nanofury/NanoFury/NF1/docs/bitfury/discreteshift.pdf

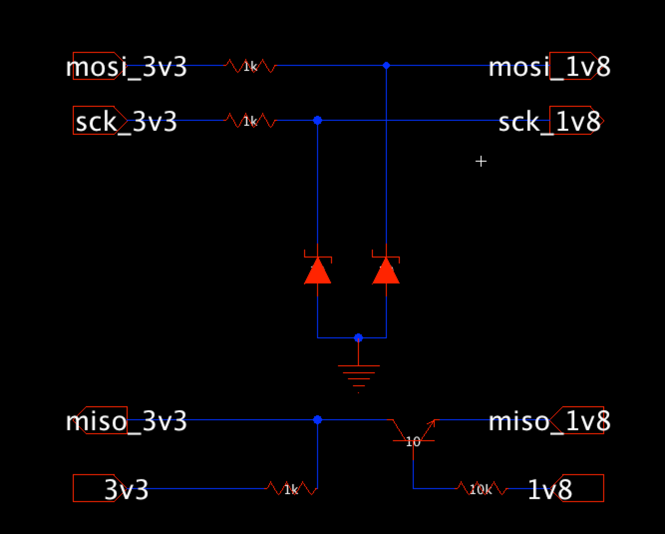
[picture p3: page 1]
