nanofury/NanoFury/NF1/kicad/NF1-MCP-V06/NF1-MCP2210-v06-PCB_Dimensions.pdf

NanoFury NF1 PCB Dimensions

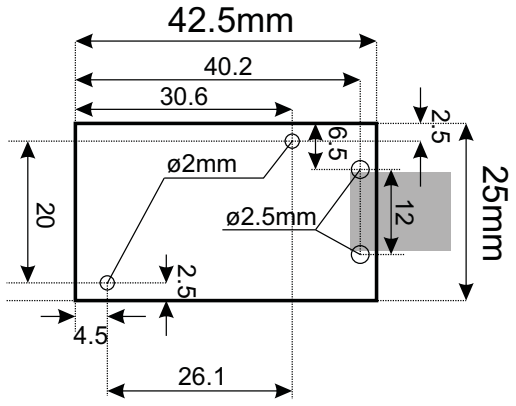
[picture p4: figure]
