nanofury/NanoFury/NF1/kicad/NF1-V0.0/NF1.png

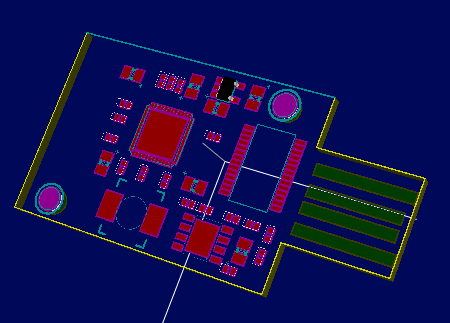
NF1/kicad/NF1-V0.0/NF1.png
