nanofury/NanoFury/NF1/docs/1001-011-01101.pdf

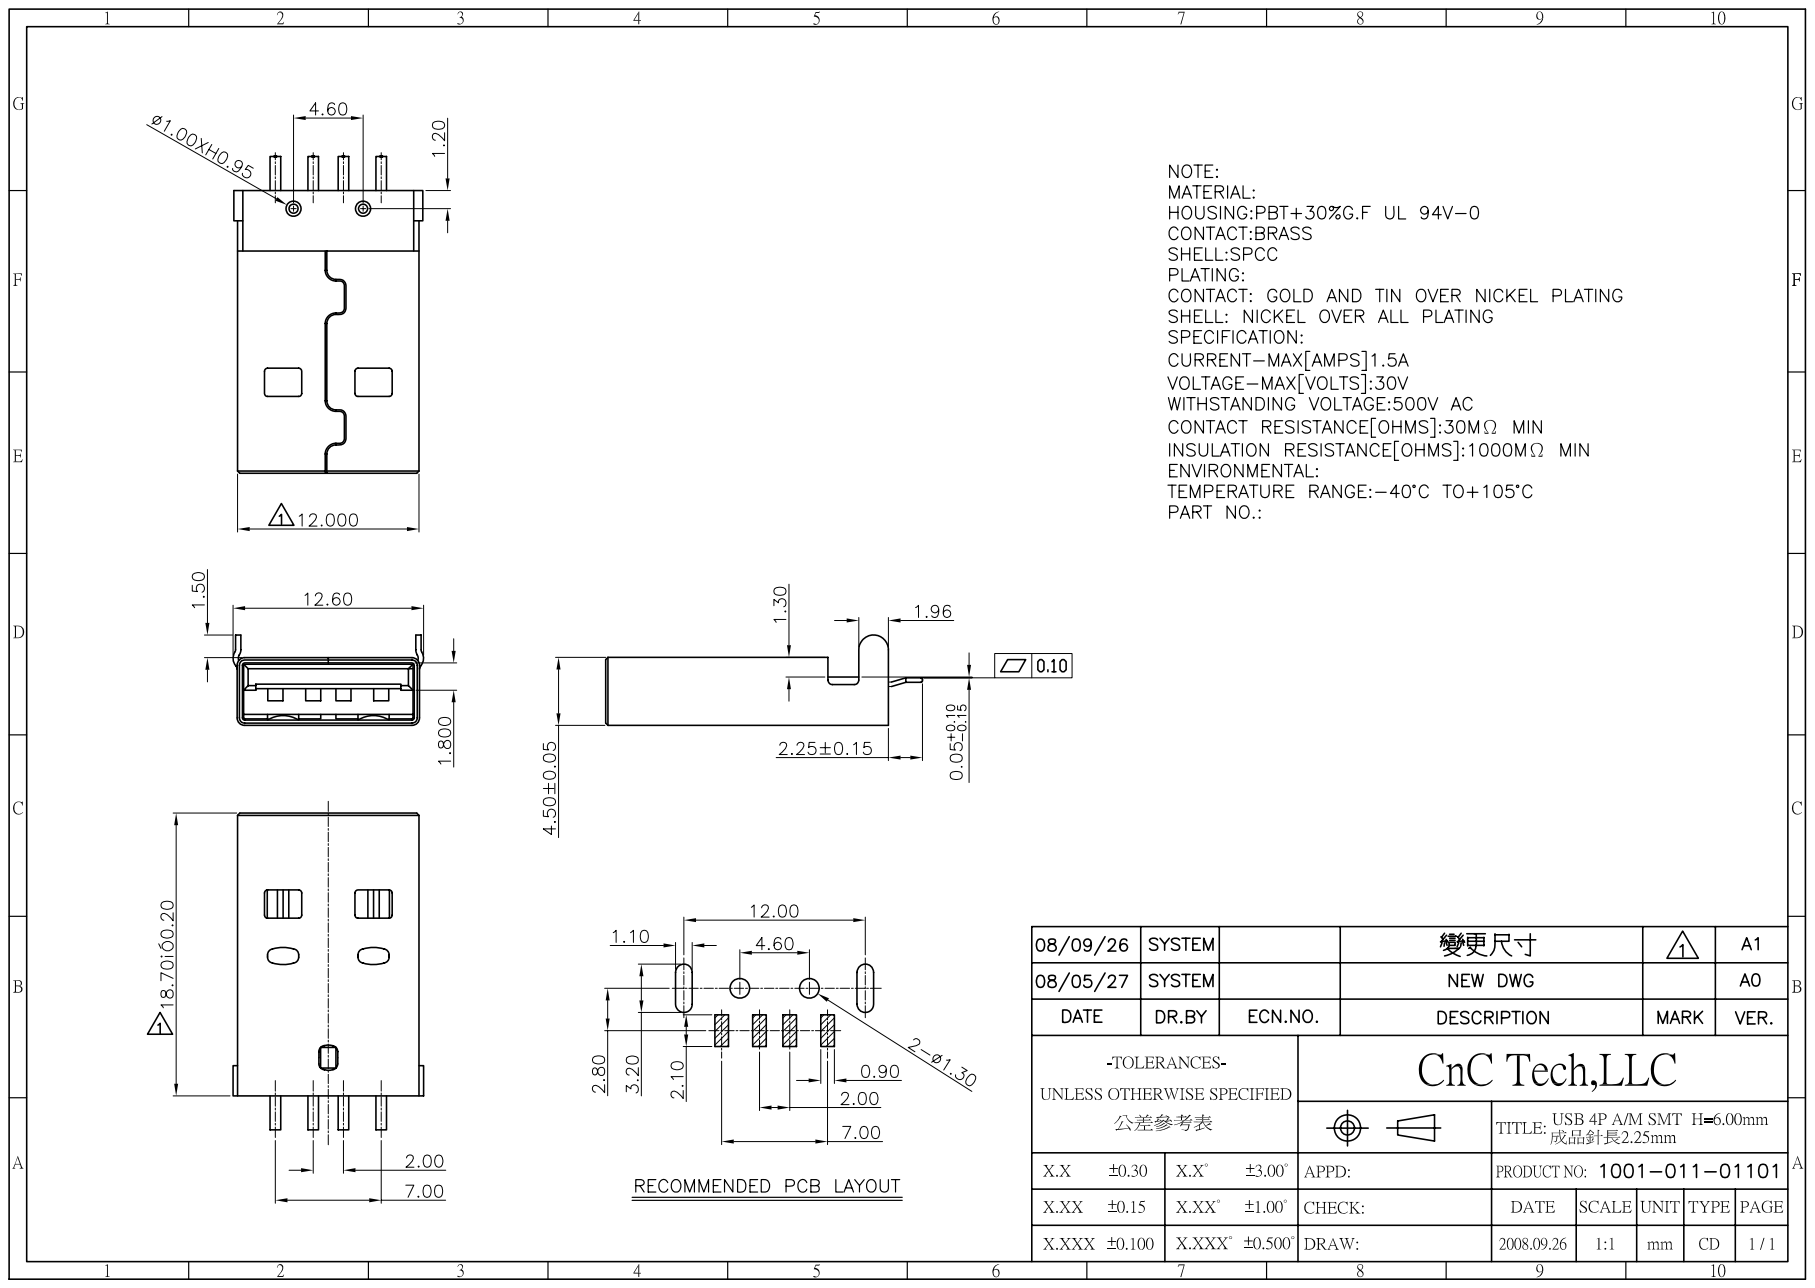
[picture p15: page 1]
