nanofury/NanoFury/NF1/kicad/NF2-MCP-V05/NF2-MCP2210-v05 - SCH.pdf

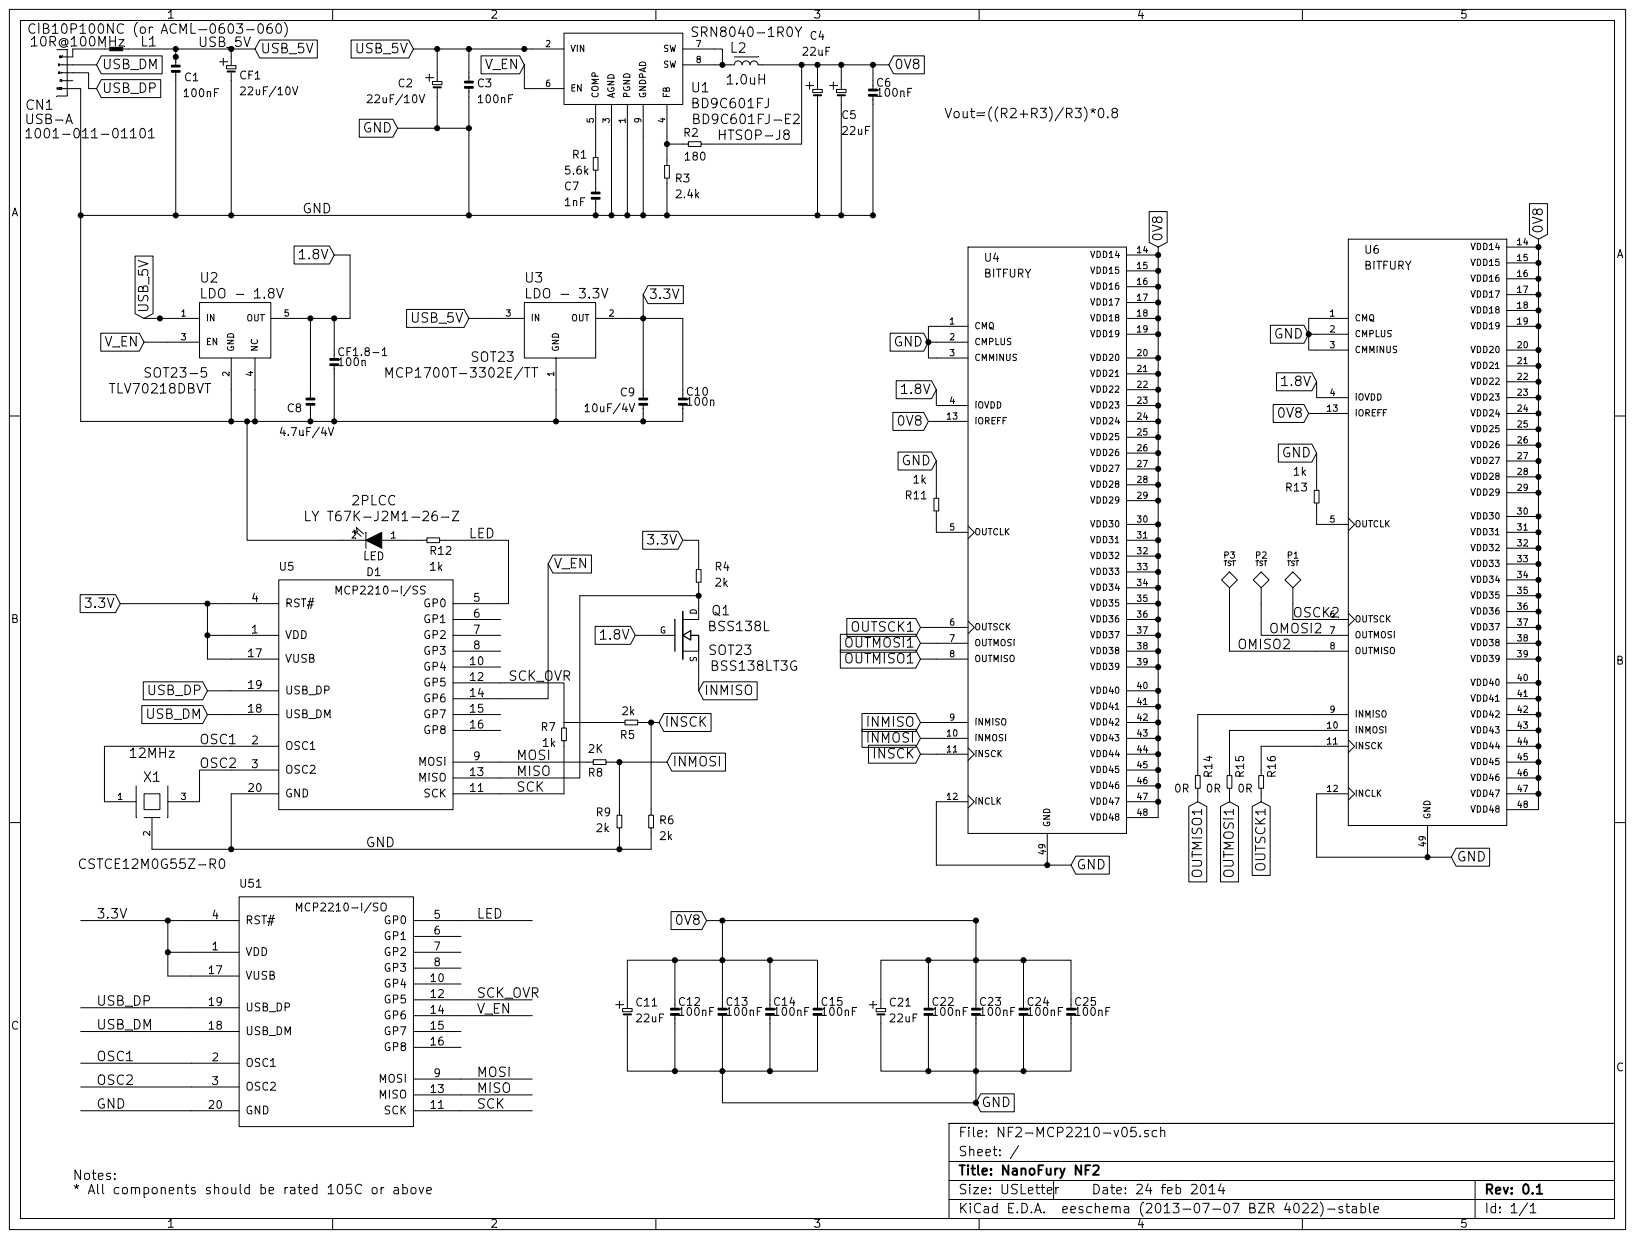
[picture p16: page 1]
