nanofury/NanoFury/NF1/kicad/NF6-MCP-V03/NF6-MCP2210-v03 - SCH.pdf

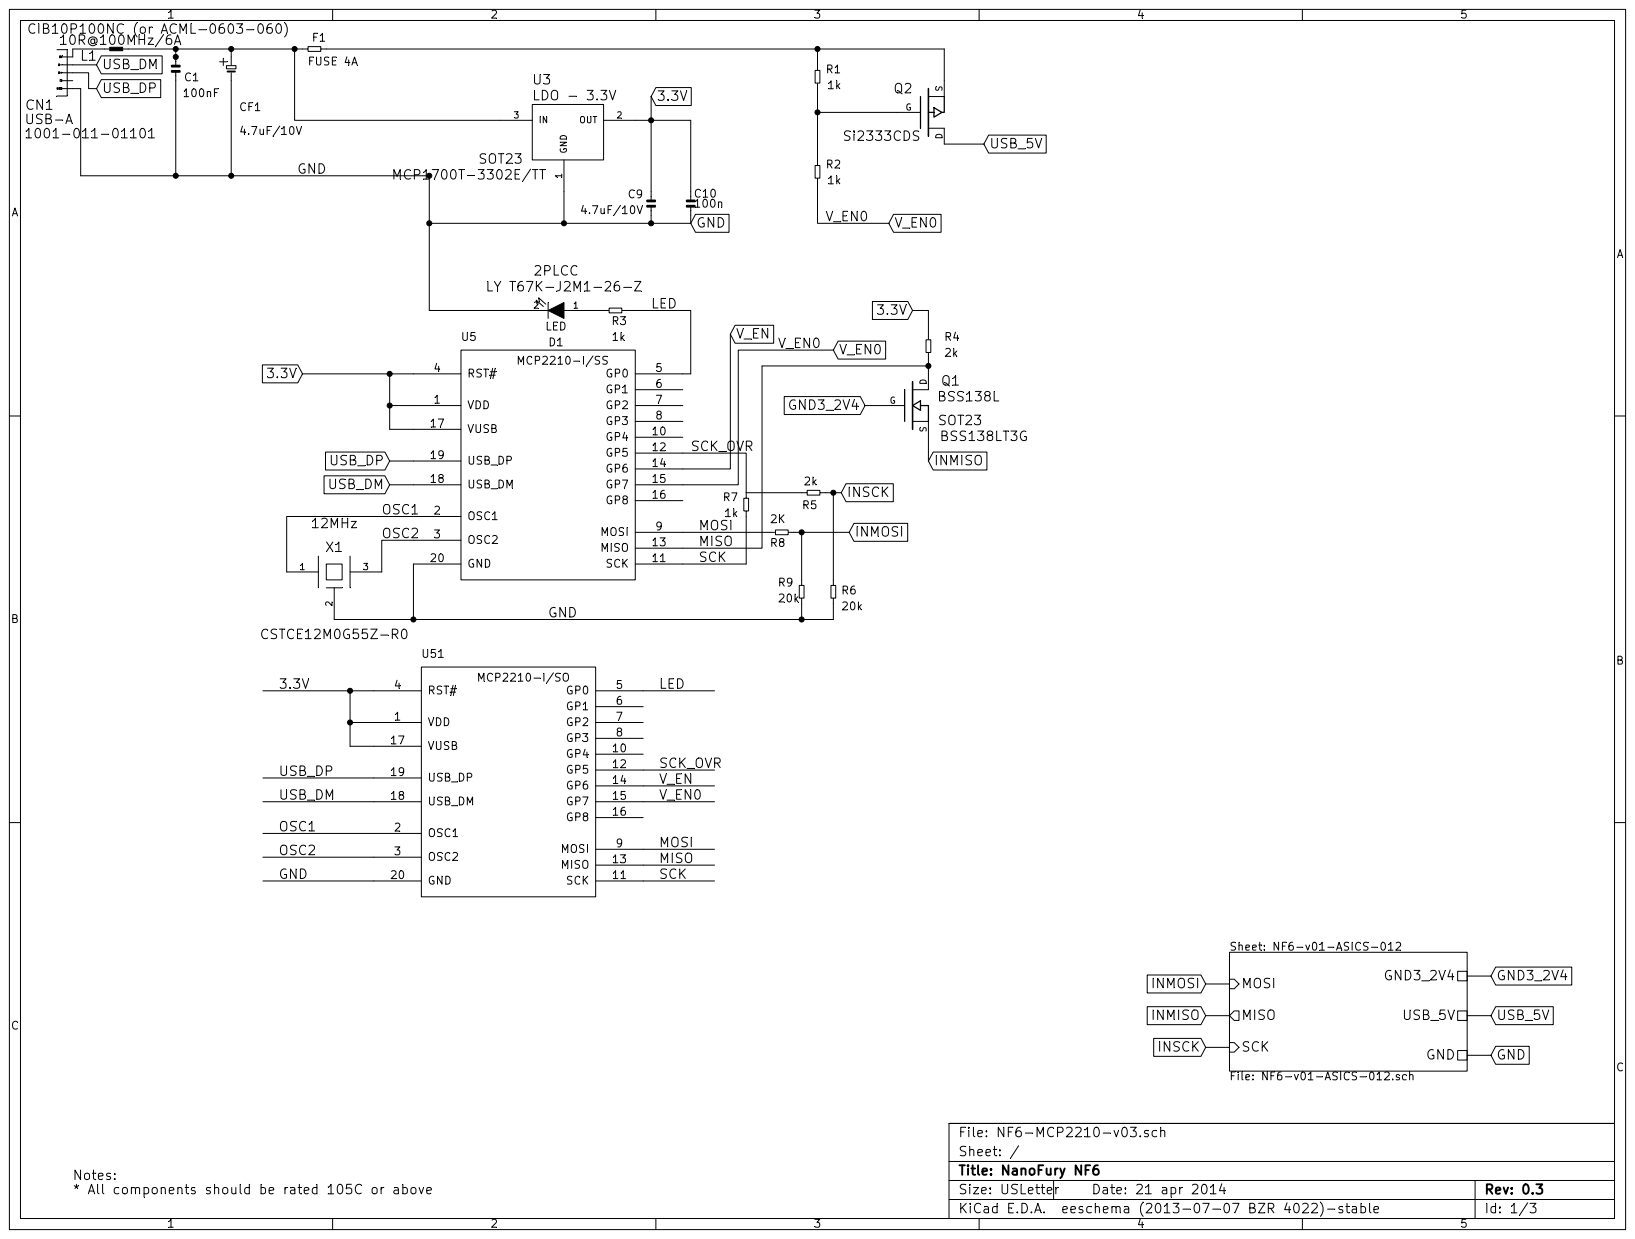
[picture p17: page 1]

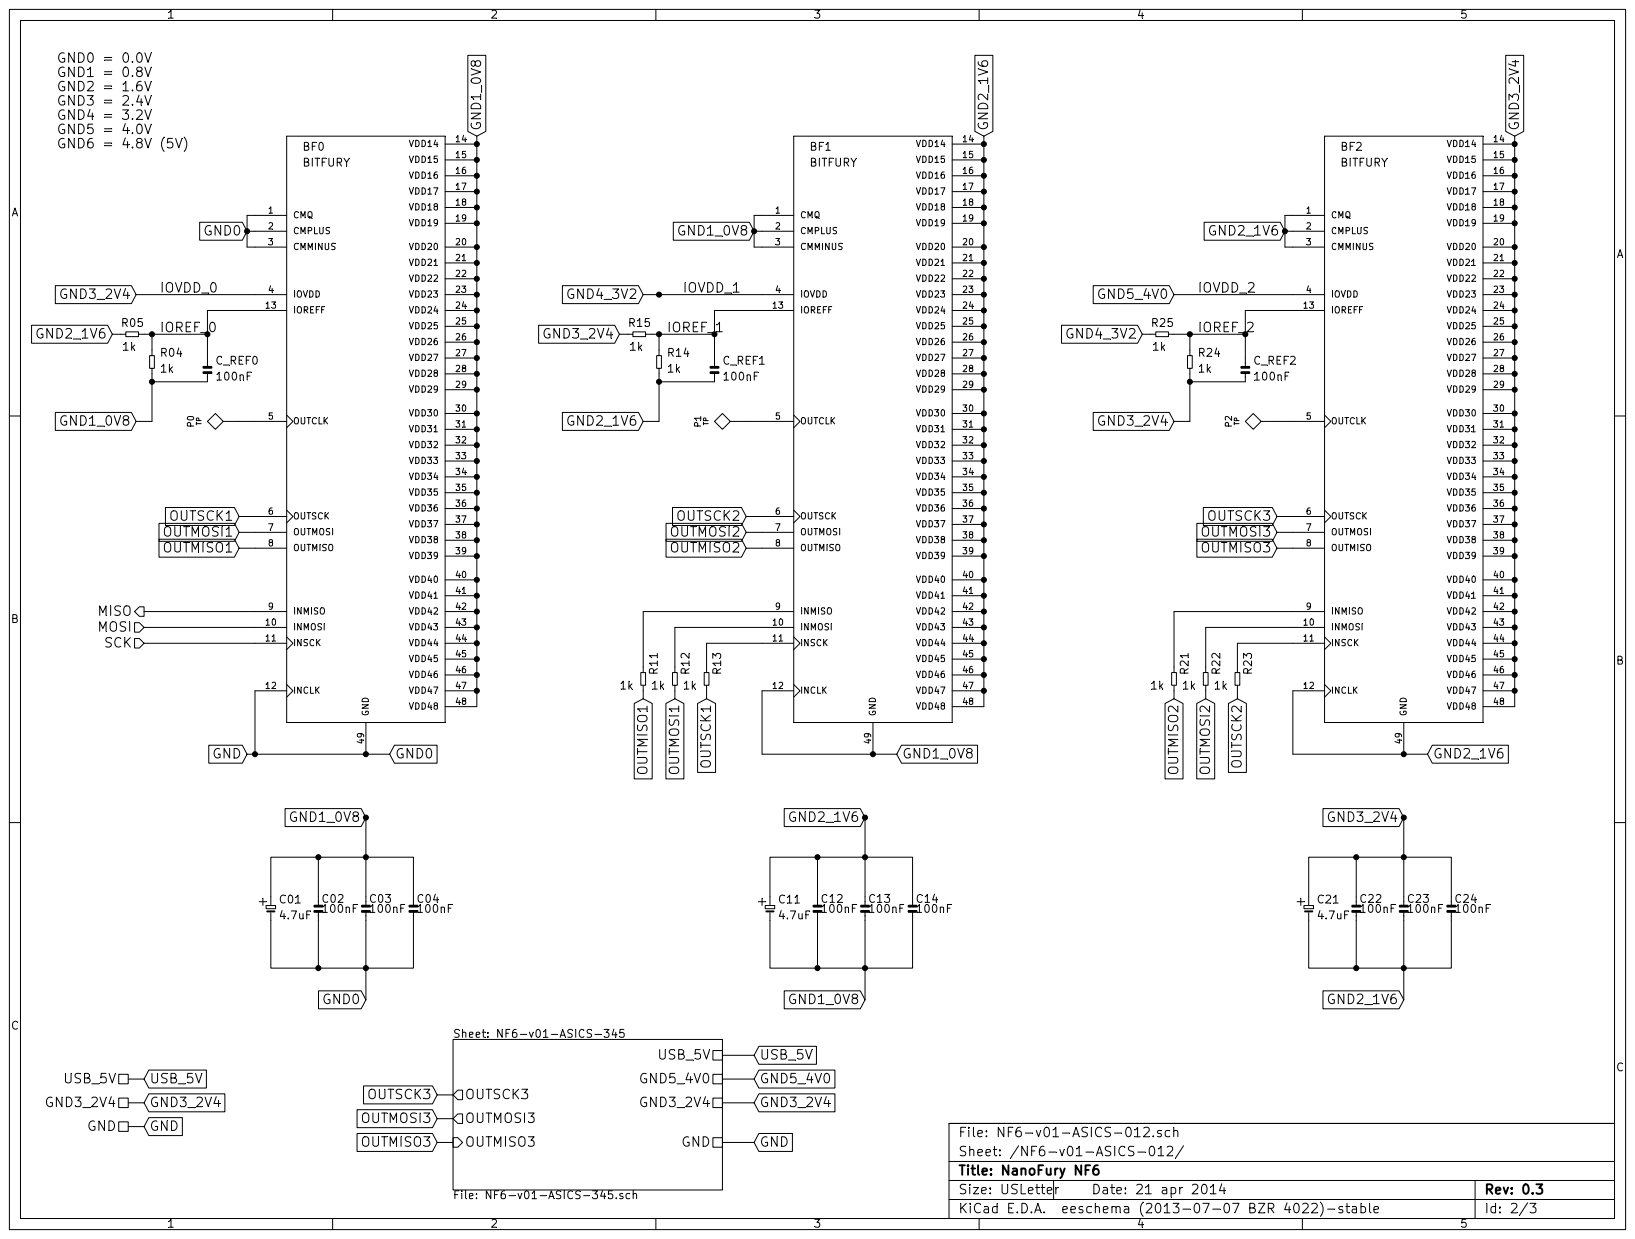
[picture p18: page 2]

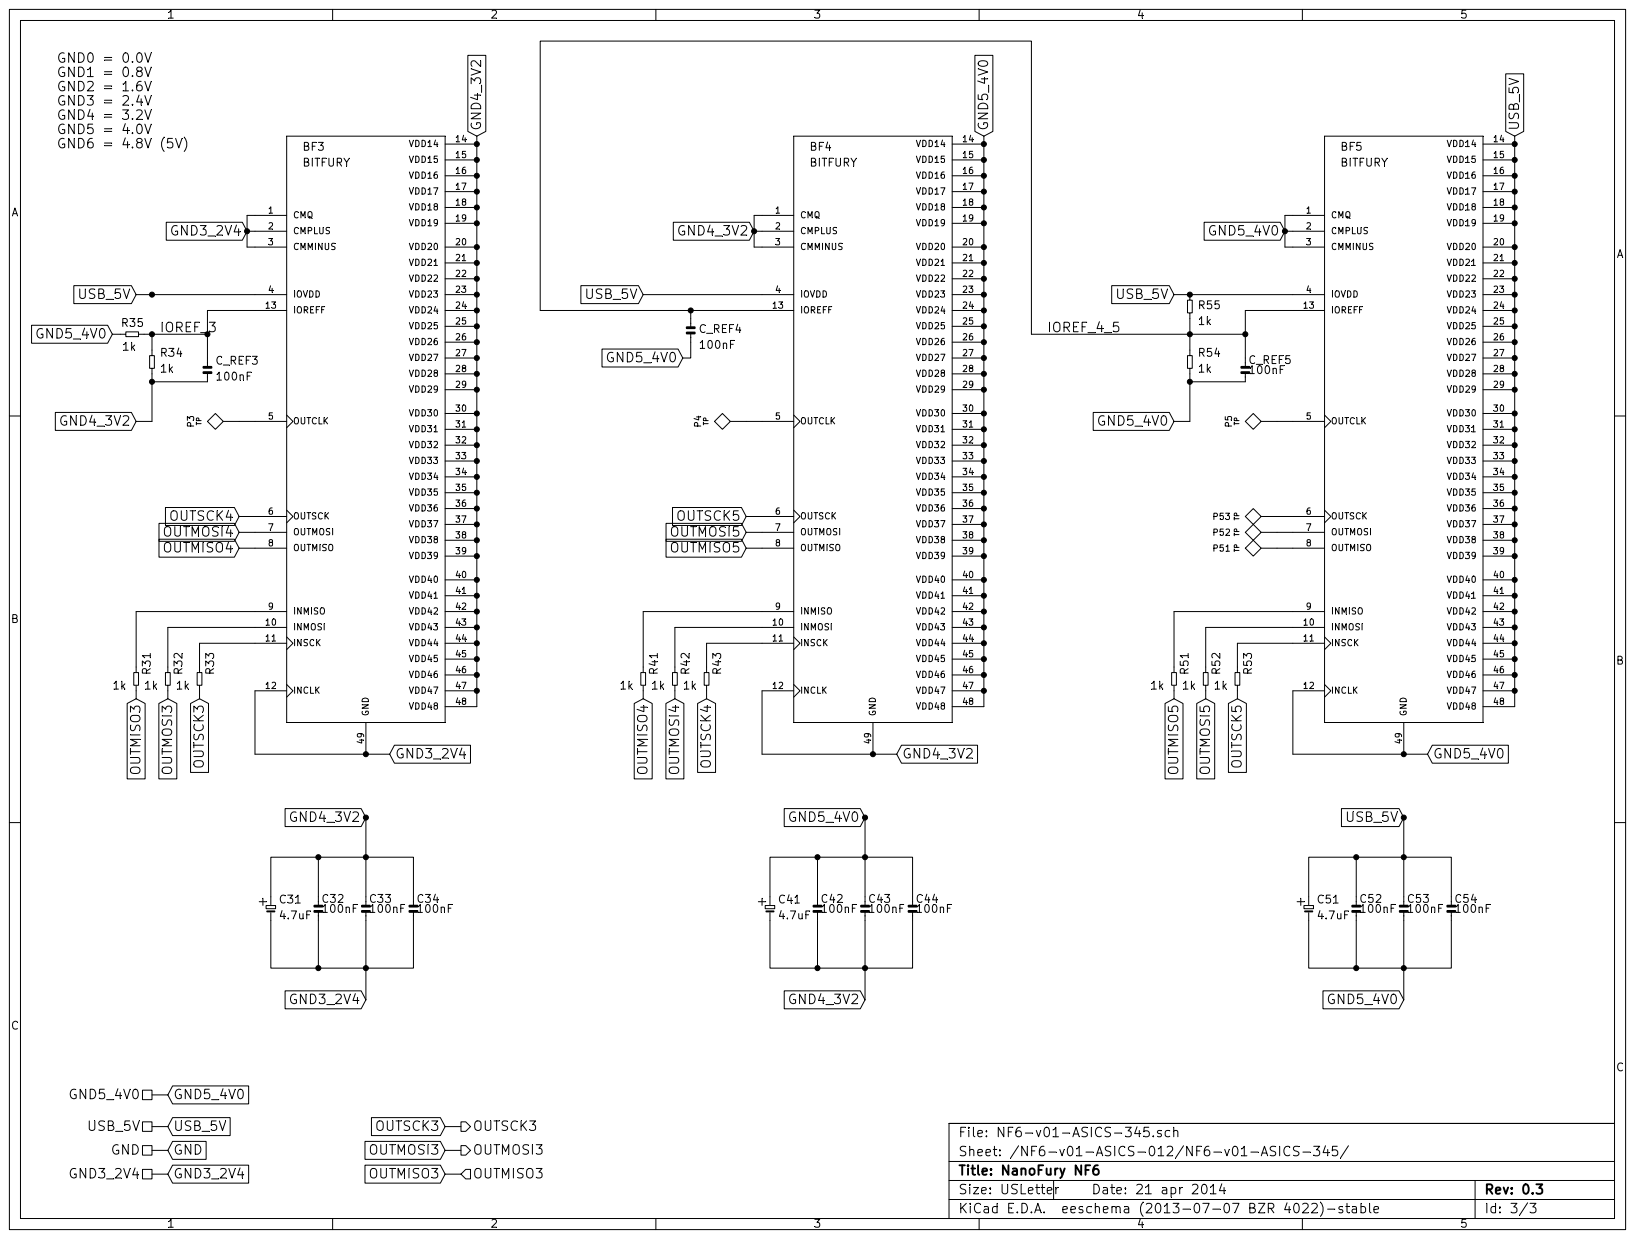
[picture p19: page 3]
