nanofury/NanoFury/NF1/kicad/NF1-MCP-V06-2/Nanofury2_Bestückungsplan.pdf

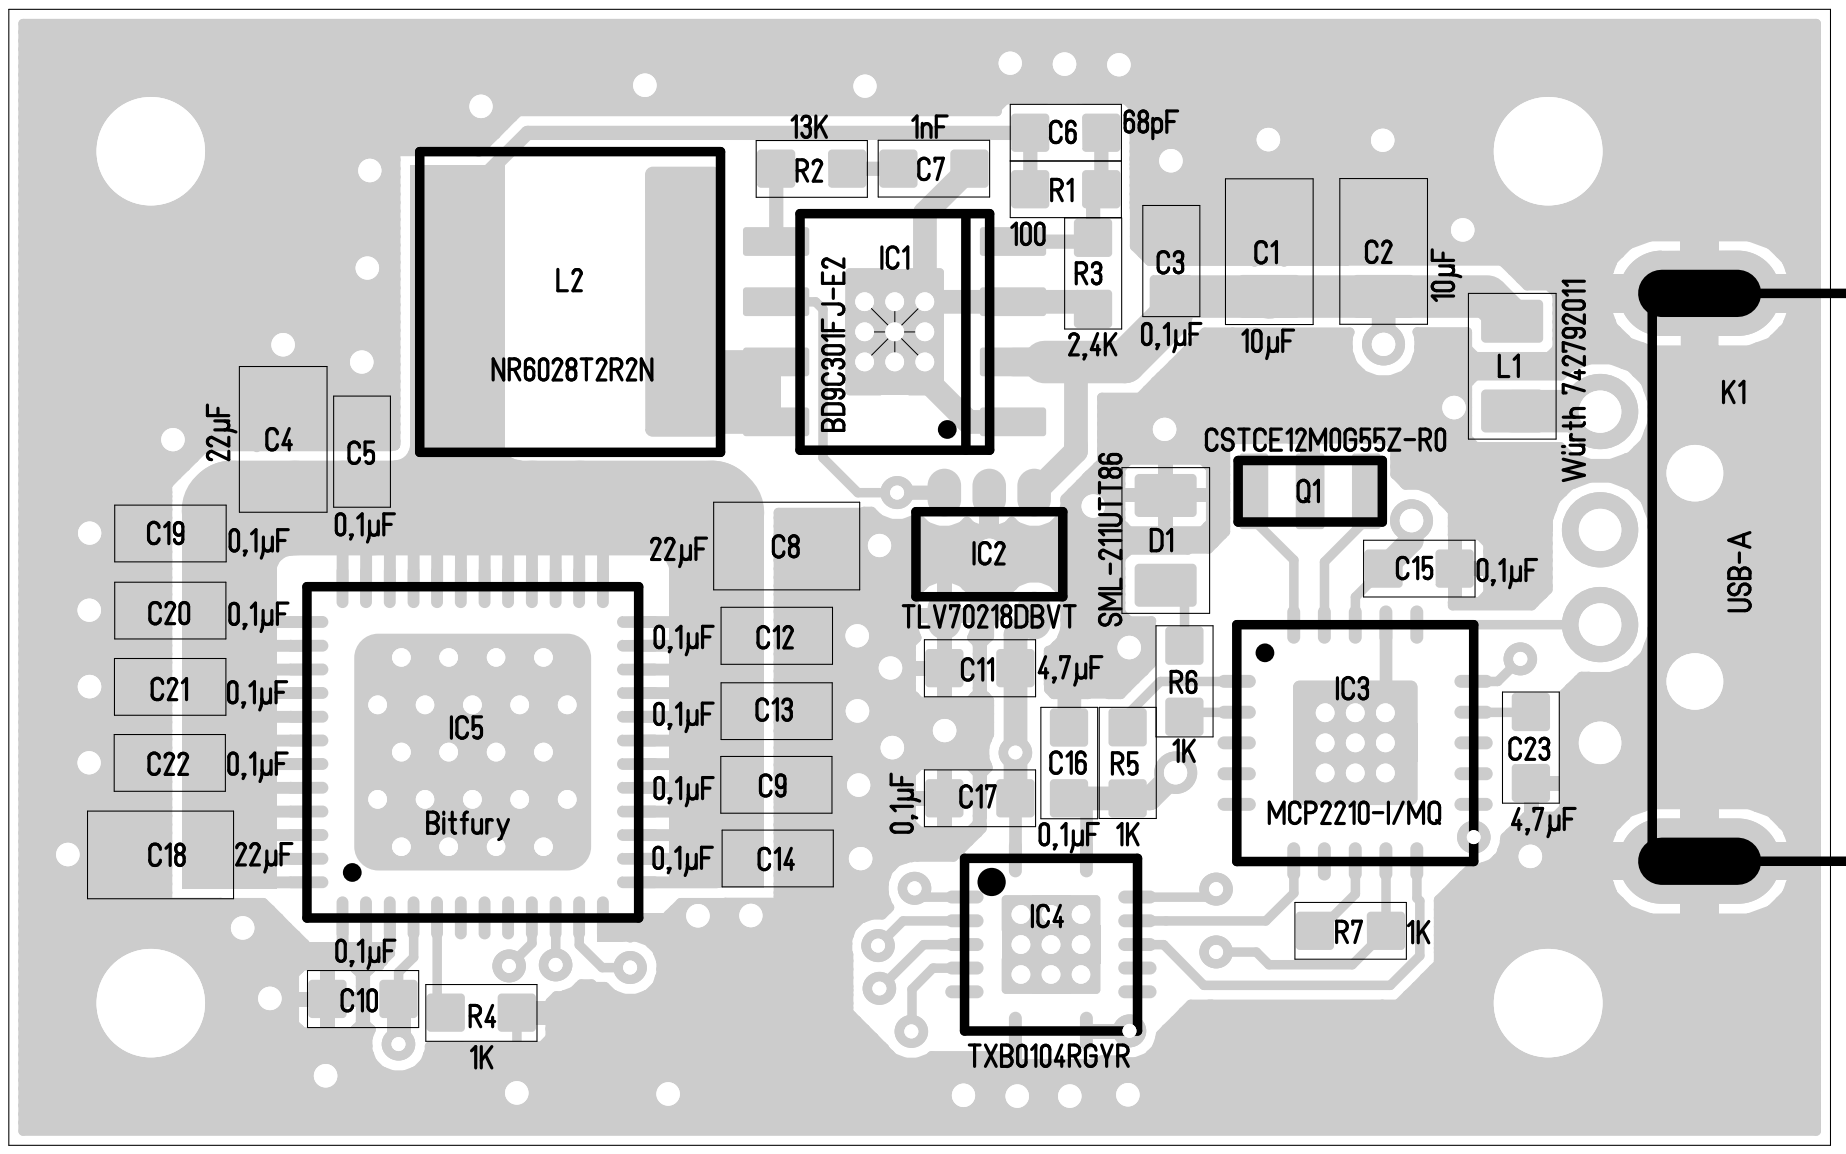
[picture p20: page 1]
