nanofury/NanoFury/NF1/kicad/NF1-MCP-V06-2/Nanofury2_Stromlaufplan.pdf

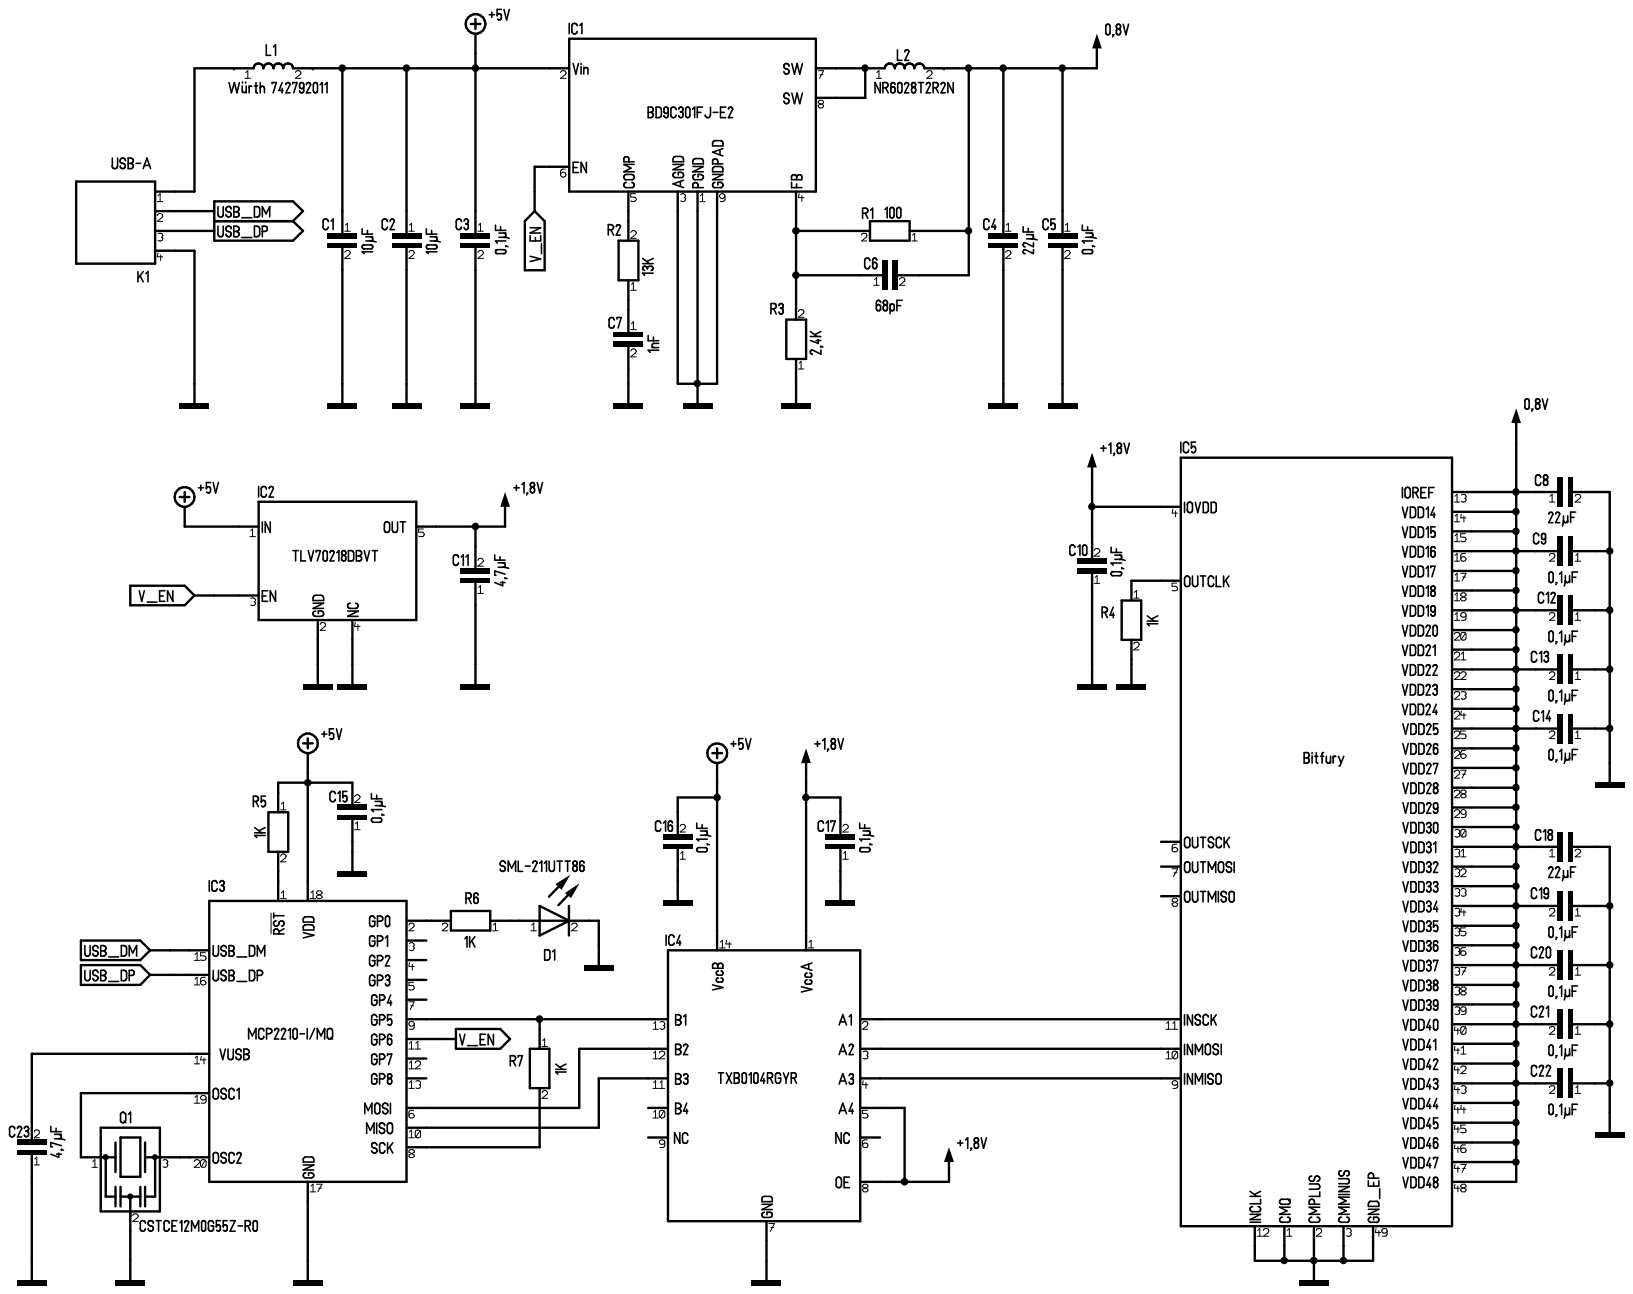
[picture p21: page 1]
