nanofury/NanoFury/NF1/kicad/NF1-MCP-V07/NF1-MCP2210-v07-SCH.pdf

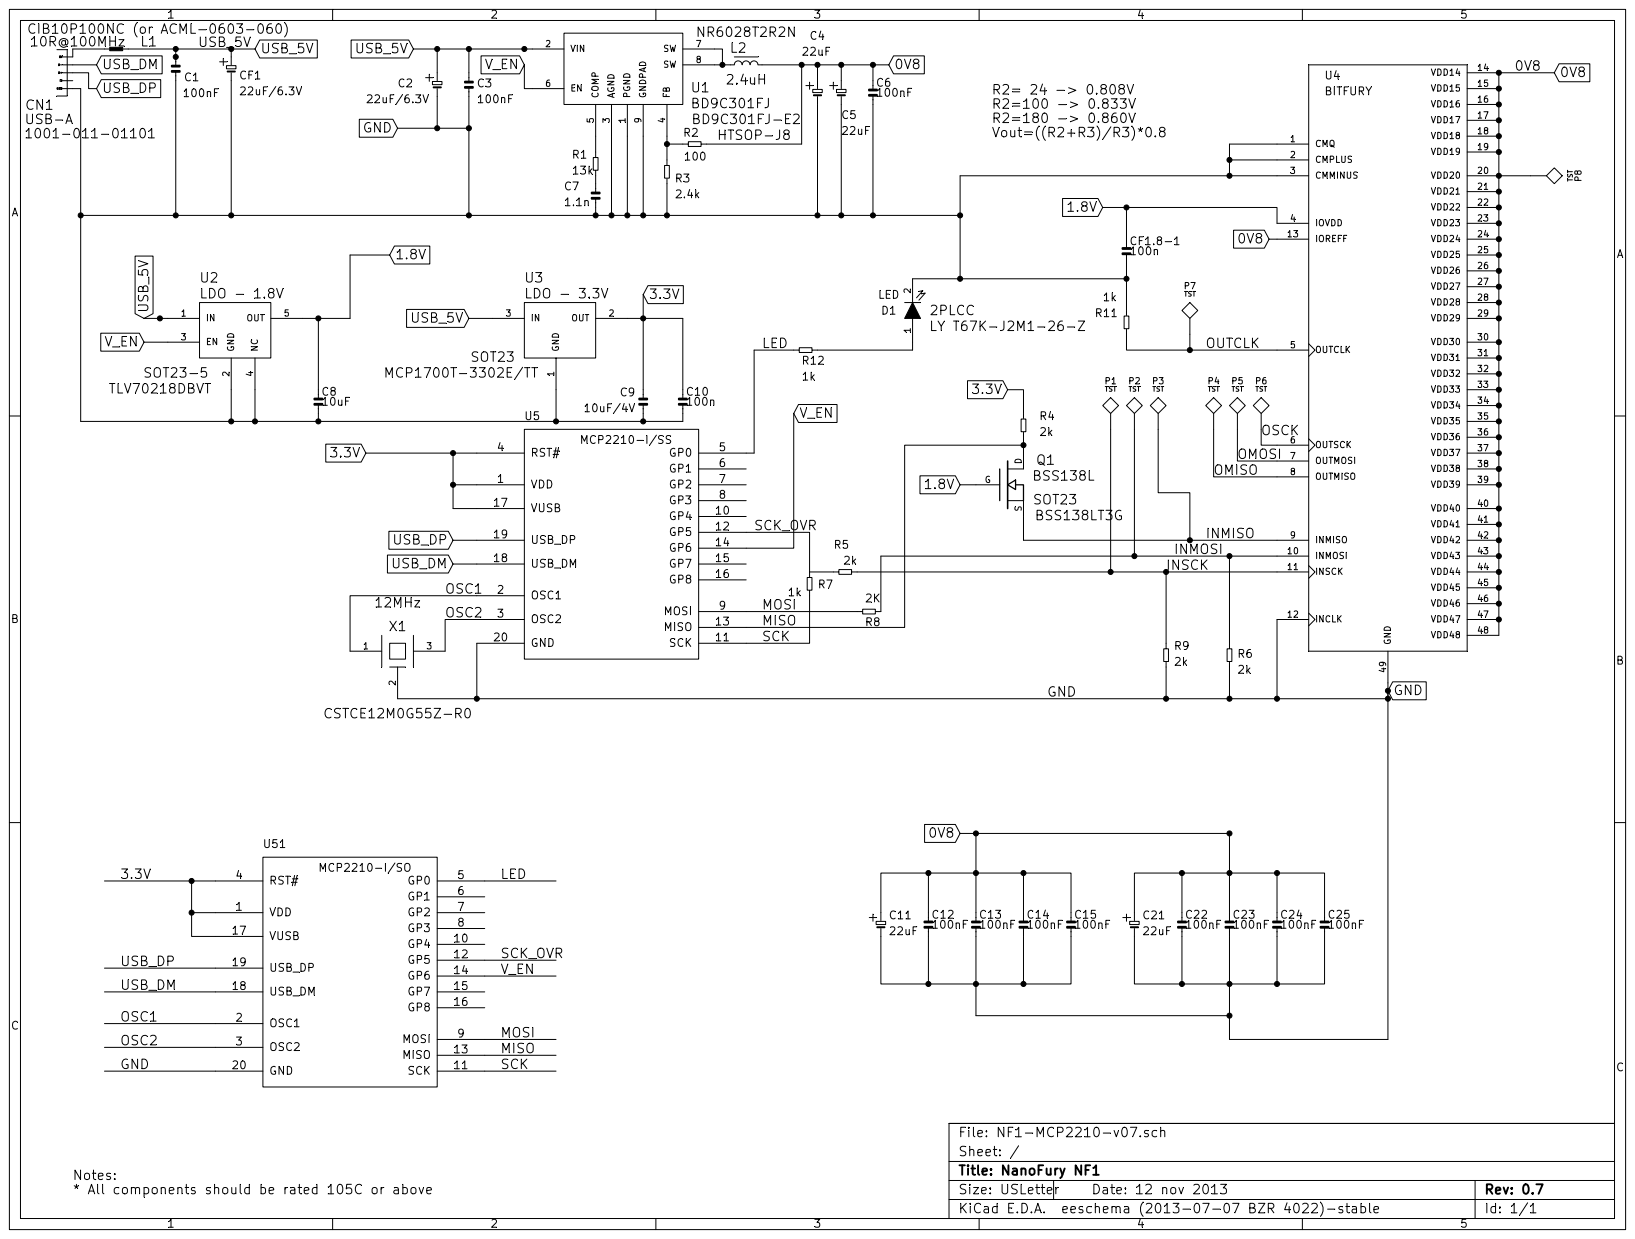
[picture p22: page 1]
