nanofury/NanoFury/NF1/kicad/NF2-MCP-V01/NF2-MCP2210-v01 - Assembly.pdf

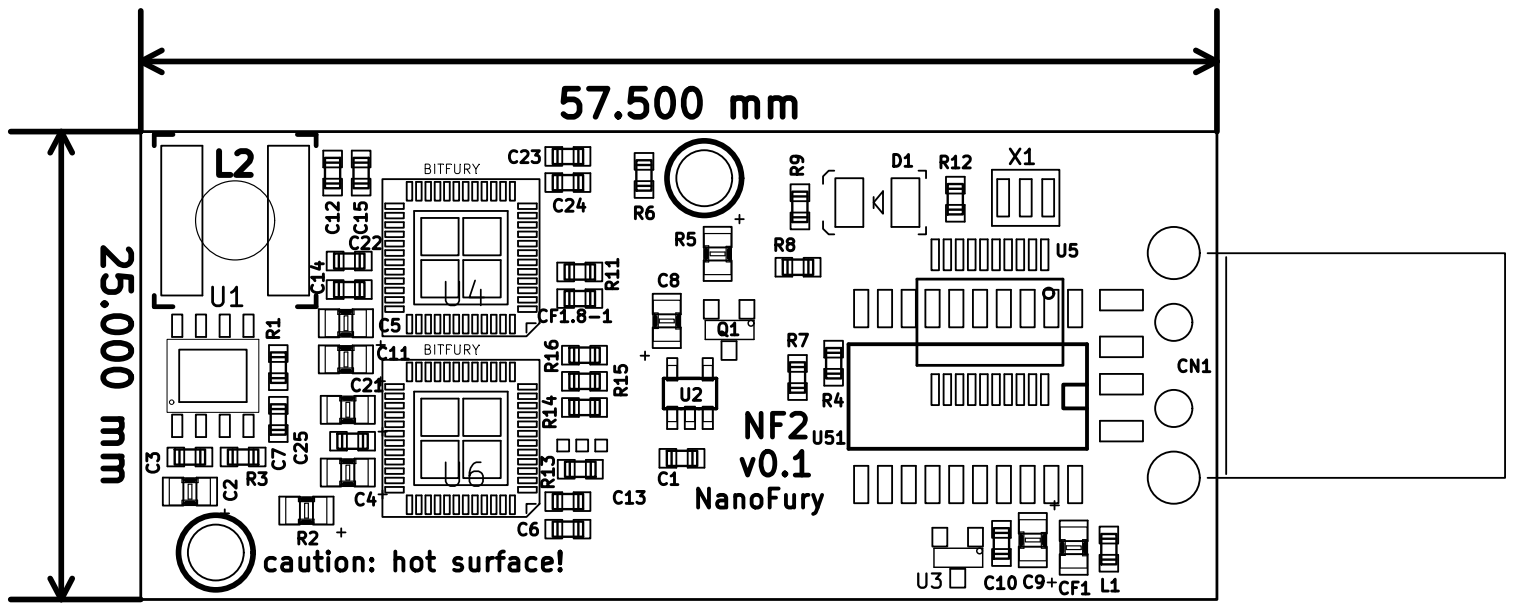
[picture p23: page 1]
