nanofury/NanoFury/NF1/kicad/NF2-MCP-V02/NF2-MCP2210-v02 - Assembly.pdf

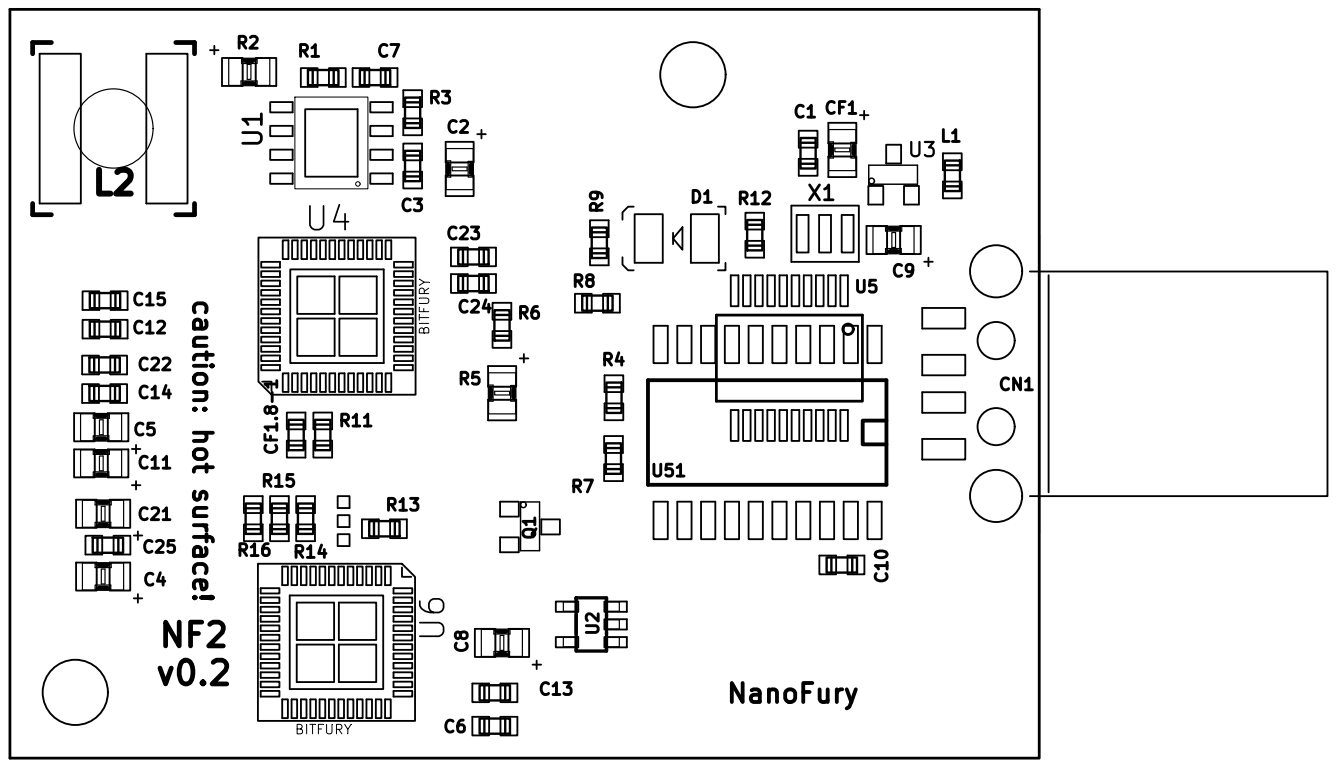
[picture p24: page 1]
