nanofury/NanoFury/NF1/kicad/NF6-MCP-V01/NF6-MCP2210-v01 - Assembly.pdf

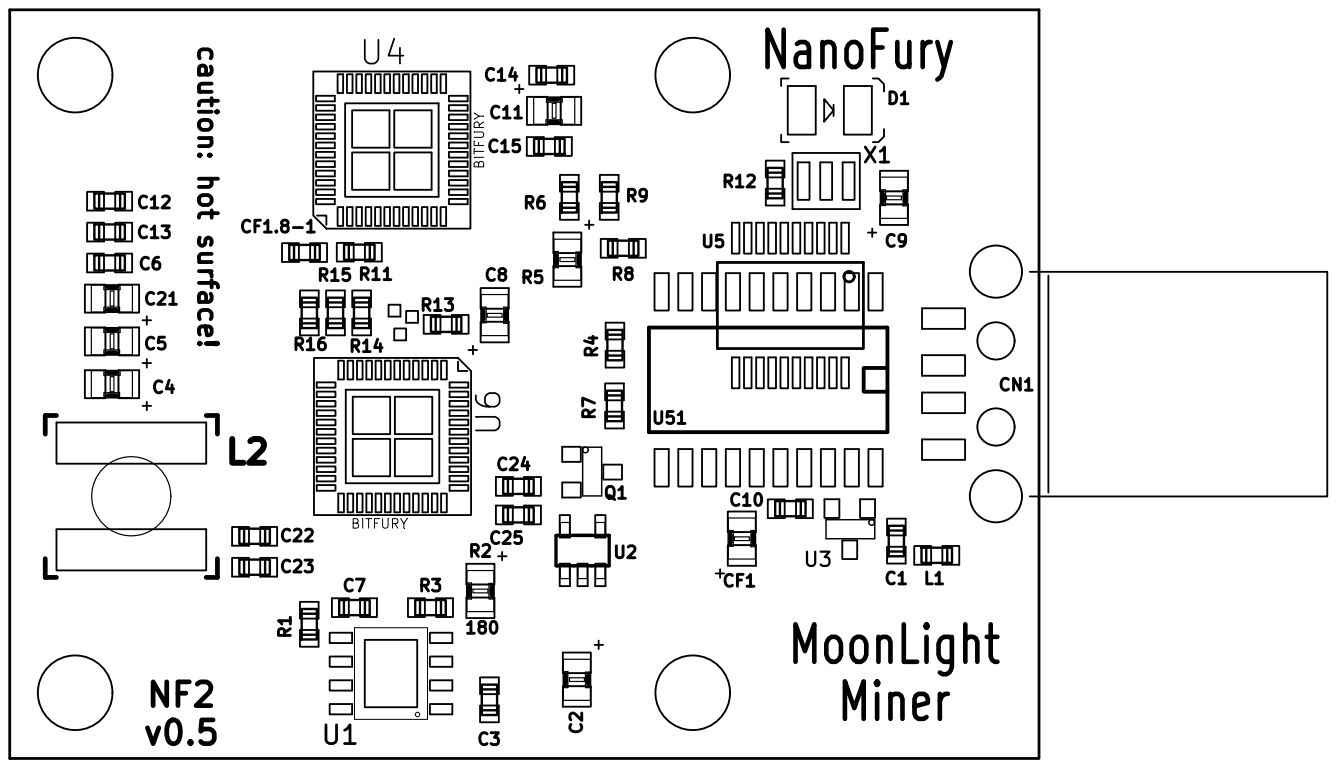
[picture p25: page 1]
