nanofury/NanoFury/NF1/kicad/NF6-MCP-V02/NF6-MCP2210-v02 - Assembly.pdf

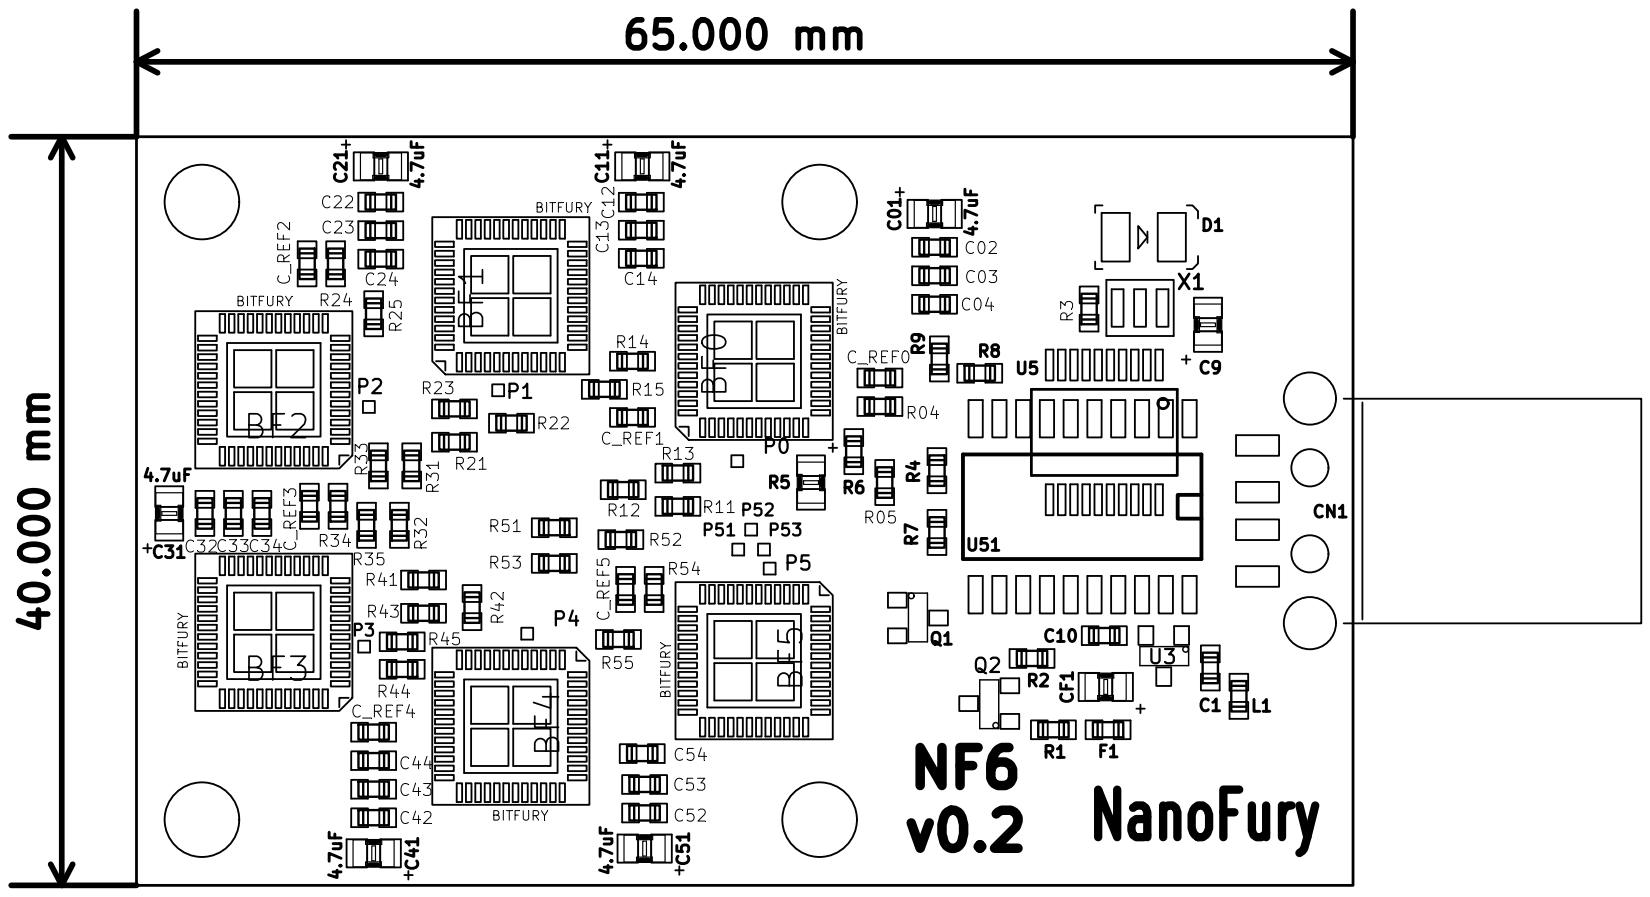
[picture p26: page 1]
