nanofury/NanoFury/NF1/kicad/NF1-MCP-V06/NF1-v0.6-assembly.pdf

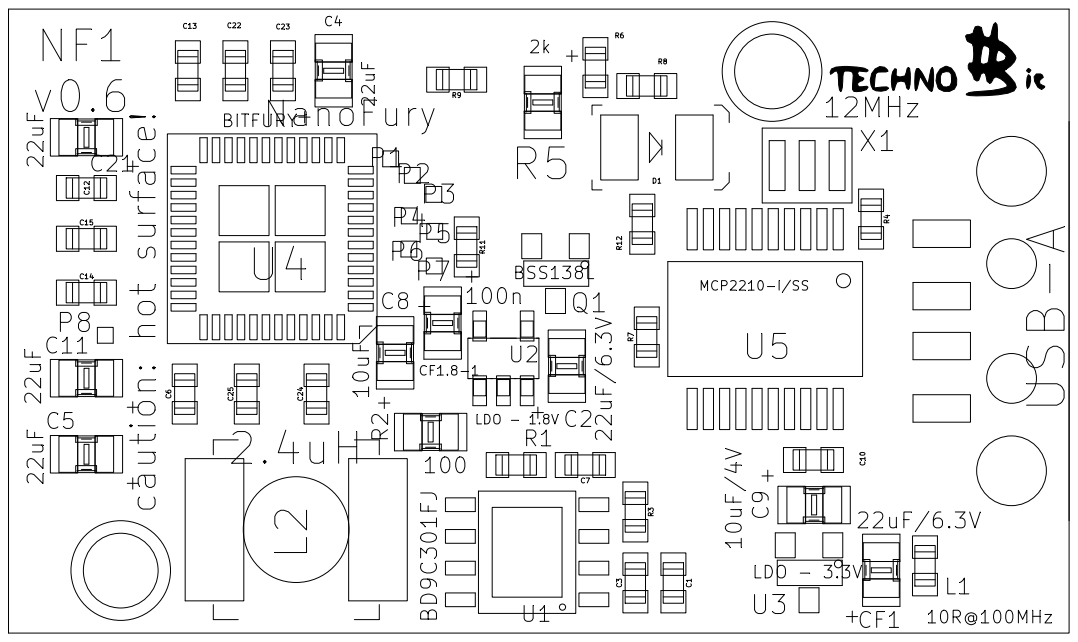
[picture p27: page 1]
