nanofury/NanoFury/NF1/kicad/NF2-MCP-V01/NF2-MCP2210-v01 - SCH.pdf

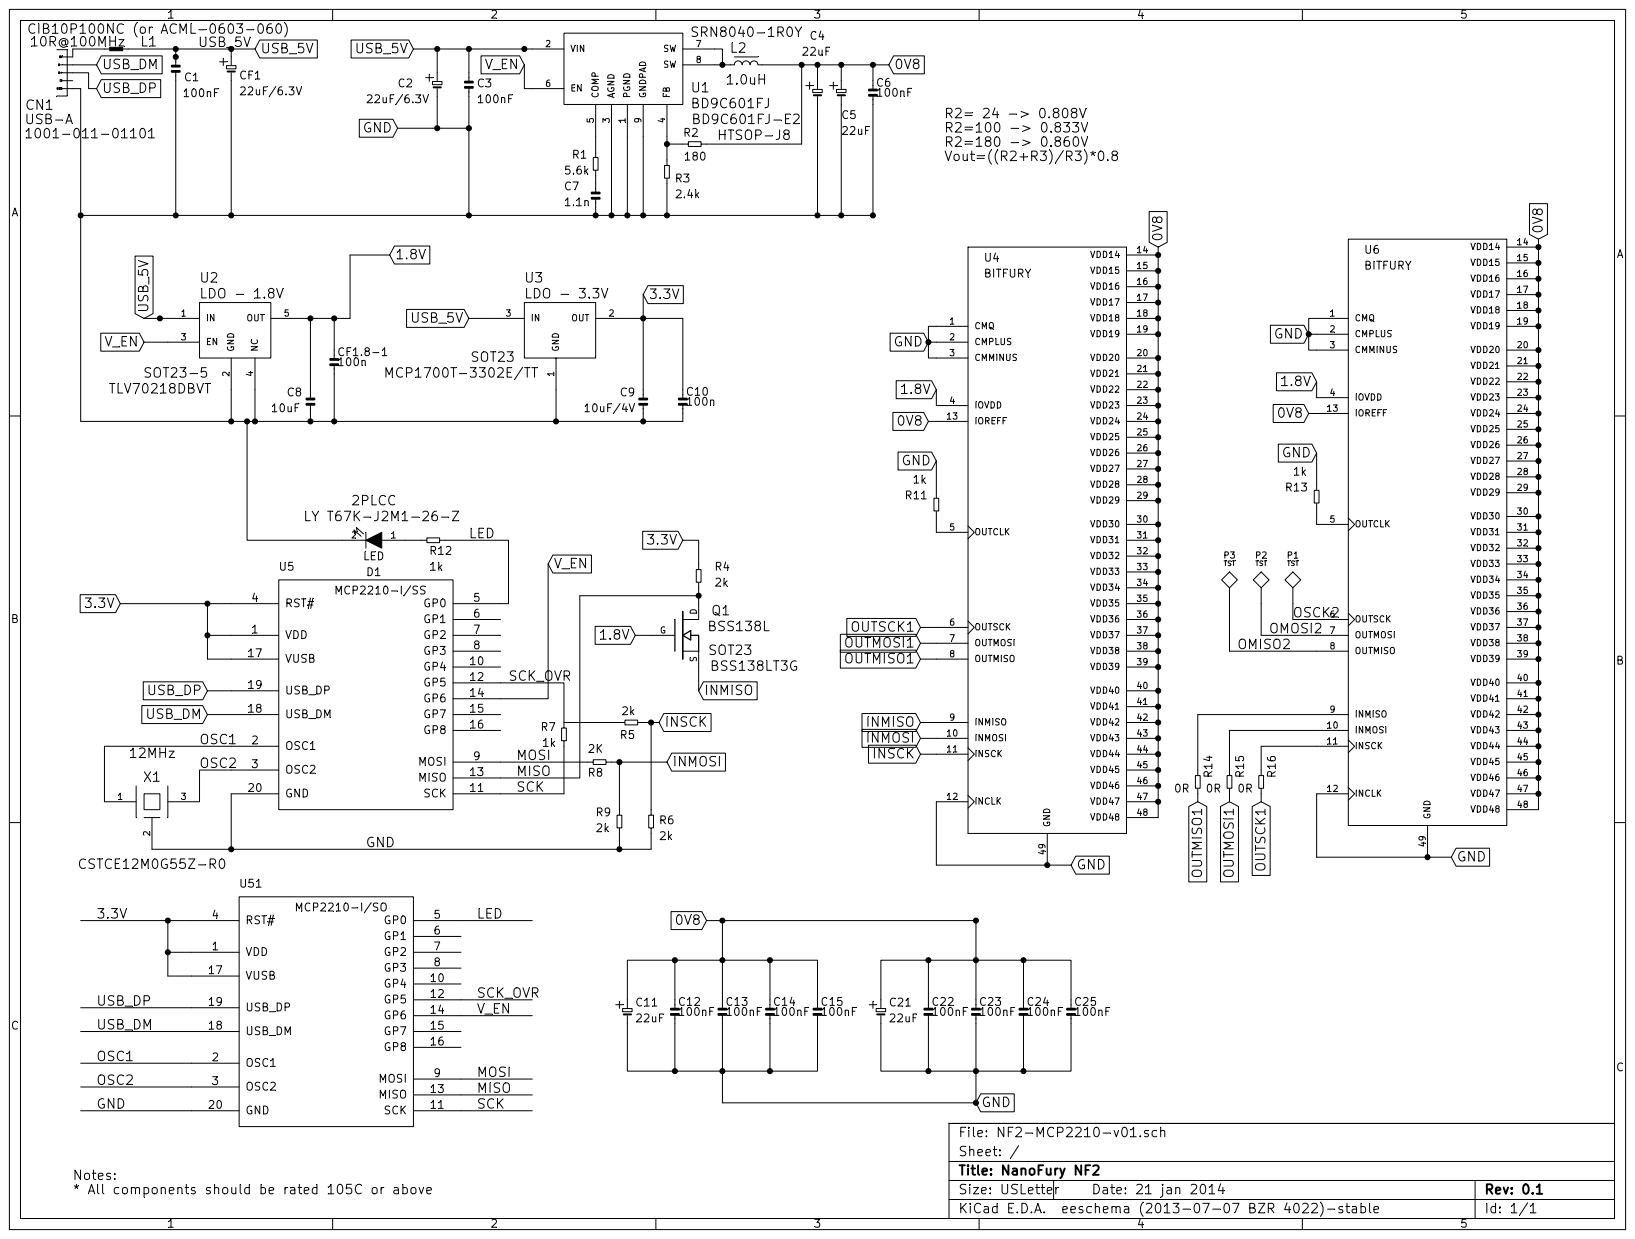
[picture p28: page 1]
