nanofury/NanoFury/NF1/kicad/NF2-MCP-V02/NF2-MCP2210-v02 - SCH.pdf

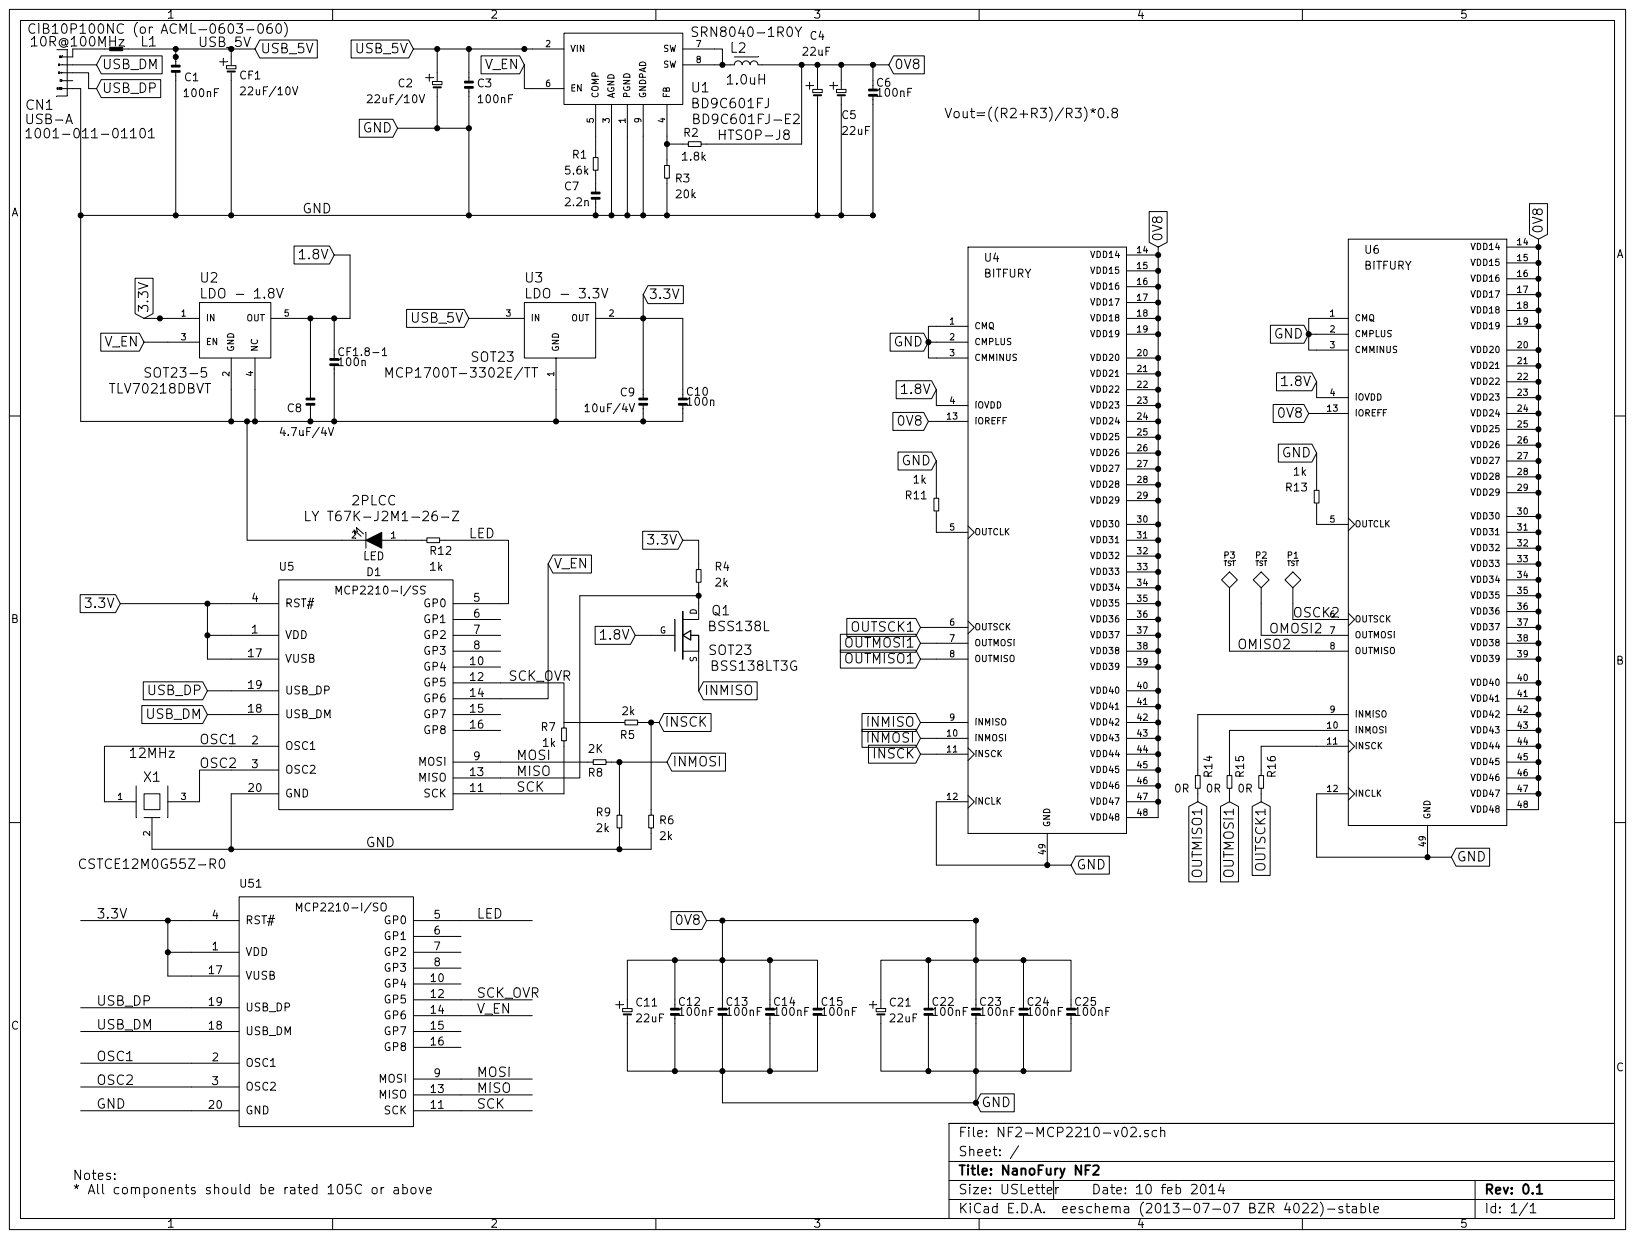
[picture p29: page 1]
