nanofury/NanoFury/NF1/kicad/NF1-MCP-V06/NF1-v0.6-sch.pdf

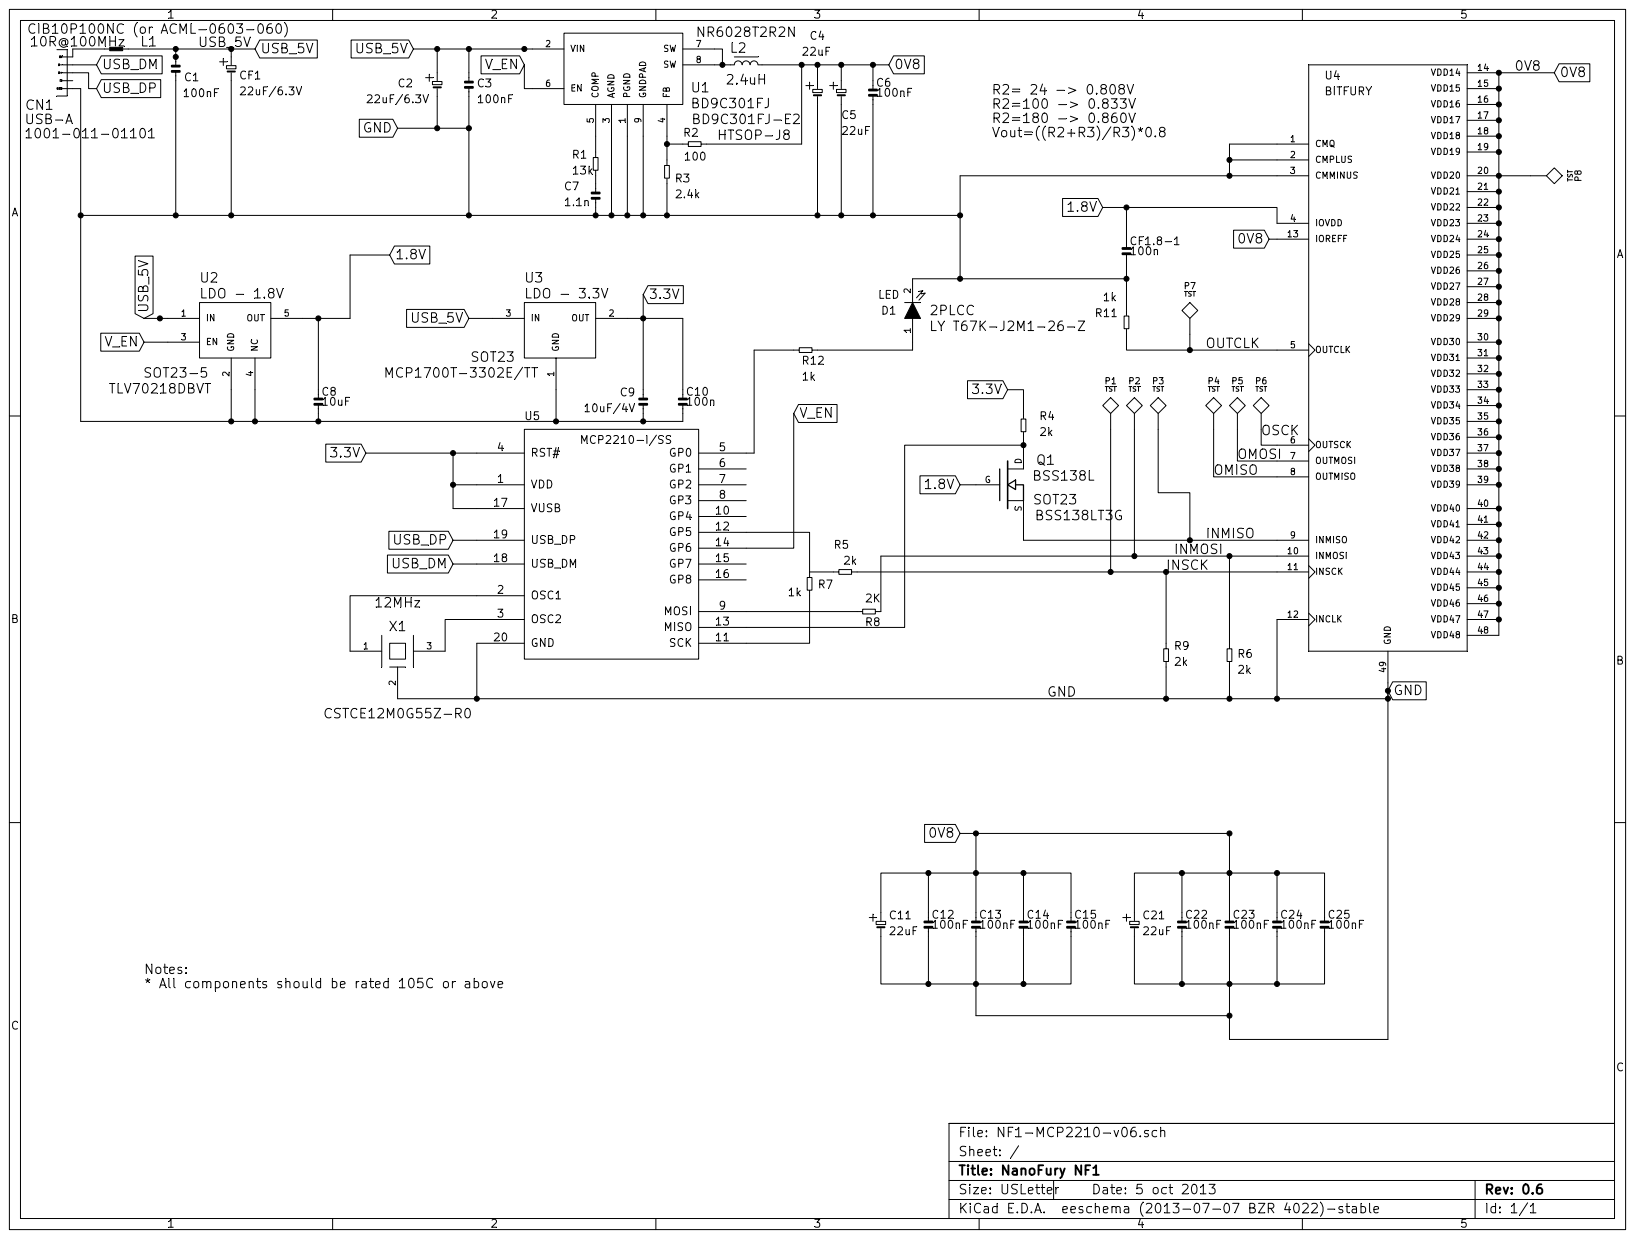
[picture p30: page 1]
